akpc806a/CAN_Logger/Firmware/IAR/demos/ARMCM4-STM32F407-DISCOVERY/main.c

/*
    ChibiOS/RT - Copyright (C) 2006-2013 Giovanni Di Sirio

    Licensed under the Apache License, Version 2.0 (the "License");
    you may not use this file except in compliance with the License.
    You may obtain a copy of the License at

        http://www.apache.org/licenses/LICENSE-2.0

    Unless required by applicable law or agreed to in writing, software
    distributed under the License is distributed on an "AS IS" BASIS,
    WITHOUT WARRANTIES OR CONDITIONS OF ANY KIND, either express or implied.
    See the License for the specific language governing permissions and
    limitations under the License.
*/

#include "ch.h"
#include "hal.h"
#include "chprintf.h"

#include "ff.h"

#include "shell.h"


#include "file_utils.h"
#include <time.h>

#include <stdio.h>
#include <limits.h>

//#define INDICATE_IDLE_ON() palSetPad(GPIOA, GPIOA_PIN5_LED_R)
//#define INDICATE_IDLE_OFF() palClearPad(GPIOA, GPIOA_PIN5_LED_R)
#define INDICATE_IDLE_ON()
#define INDICATE_IDLE_OFF()

uint8_t bButton = 0;
unsigned char bLogging = 0; // if =1 than we logging to SD card

//------------------------------------------------------------------------------
// CAN instance configuration
static CANConfig cancfg = {
  CAN_MCR_ABOM | CAN_MCR_AWUM,
  CAN_BTR_SJW(0) | CAN_BTR_TS2(2) |
  CAN_BTR_TS1(1) | CAN_BTR_BRP(13)
};


//------------------------------------------------------------------------------

/*===========================================================================*/
// data bufferization functions

#define SD_WRITE_BUFFER             (1024*49)//(1024*21)   // 21K
#define SD_WRITE_BUFFER_FLUSH_LIMIT (1024*48)//(1024*20)   // 20K

#include <string.h>
#include "mmcsd.h"

// buffer for collecting data to write
char sd_buffer[SD_WRITE_BUFFER];
WORD sd_buffer_length = 0;

// buffer for storing ready to write data
char sd_buffer_for_write[SD_WRITE_BUFFER];
unsigned char bReqWrite = 0; // write request, the sd_buffer is being copied to sd_buffer_for_write 
WORD sd_buffer_length_for_write = 0;

unsigned char bWriteFault = 0; // in case of overlap or write fault


// fill buffer with spaces (before \r\n) to make it 512 byte size
// return 1 if filled and ready to write
int align_buffer()
{
  int i;
  int len;
  
  if (sd_buffer_length < 2) return 0;
  if (sd_buffer[sd_buffer_length-2] != '\r') return 0;
  if (sd_buffer[sd_buffer_length-1] != '\n') return 0;
  
  len = MMCSD_BLOCK_SIZE - (sd_buffer_length % MMCSD_BLOCK_SIZE);
  for (i = 0; i < len; i++)
    sd_buffer[sd_buffer_length + i - 2] = ' ';
  sd_buffer[sd_buffer_length - 2] = ',';
  sd_buffer[sd_buffer_length + len - 2] = '\r';
  sd_buffer[sd_buffer_length + len - 1] = '\n';
  
  sd_buffer_length += len;
  
  return 1;
}

// copy input buffer into the buffer for flash writing data
void copy_buffer()
{
  // request write operation
  memcpy(sd_buffer_for_write, sd_buffer, sd_buffer_length);
  sd_buffer_length_for_write = sd_buffer_length;
  sd_buffer_length = 0;
}

void request_write()
{
  chSysLock(); // prevent re-entry
  
  if (bReqWrite)
    bWriteFault = 1; // buffer overlapping
  
  // request write operation
  align_buffer();
  copy_buffer();
  bReqWrite = 1;
  
  chSysUnlock(); // leaving critical section
}

int iLastWriteSecond = 0;
static struct tm timp;
  
void fwrite_string(char *pString)
{
  WORD length = strlen(pString);

  // Add string
  memcpy(&sd_buffer[sd_buffer_length], pString, length);
  sd_buffer_length += length;
  
  // Check flush limit
  if(sd_buffer_length >= SD_WRITE_BUFFER_FLUSH_LIMIT)
  {
    request_write();
  }
}





// file writing 
FATFS SDC_FS;
FIL *file;
FRESULT fres;

int i;
int iSecond;
#define STRLINE_LENGTH 1024
char sLine[STRLINE_LENGTH];
systime_t stLastWriting;
unsigned char bIncludeTimestamp = 1;

void start_log(int file_index, char* file_name)
{
  // open file and write the begining of the load
  if (file_index >= 0)
  {
    sprintf(sLine, "%d.csv", file_index);
  }
  else if (file_name != 0)
  {
    sprintf(sLine, "%s.csv", file_name);
  }
  else
  {
    rtcGetTimeTm(&RTCD1, &timp);        
    sprintf(sLine, "%02d-%02d-%02d.csv", timp.tm_hour, timp.tm_min, timp.tm_sec);
  }
  
  file = fopen_(sLine, "a");
  if (bIncludeTimestamp)
    strcpy(sLine, "Timestamp,ID,Data0,Data1,Data2,Data3,Data4,Data5,Data6,Data7\r\n");
  else
    strcpy(sLine, "ID,Data0,Data1,Data2,Data3,Data4,Data5,Data6,Data7\r\n");
  fwrite_string(sLine);
  align_buffer();
  fwrite_(sd_buffer, 1, sd_buffer_length, file);
  f_sync(file);

  // reset buffer counters
  sd_buffer_length_for_write = 0;
  sd_buffer_length = 0;

  bWriteFault = 0;

  stLastWriting = chTimeNow(); // record time when we did write

  bLogging = 1;
}

int iFilterMask = 0;
int iFilterValue = 0;
unsigned char bLogStdMsgs = 1;
unsigned char bLogExtMsgs = 1;

unsigned char bAutoStart = 0;
unsigned char bCircularWriting = 0;
unsigned char bStartOnCAN = 0;
unsigned char bStopOnCAN = 0;
int iIDStartValue = 0;
int iIDStartMask = 0;
unsigned char bStartFrameToName = 0;
int iIDStopValue = 0;
int iIDStopMask = 0;

int iLastFileName = 0; // the file name index from file 


int read_config_file()
{
  int value;
  char name[128];
  char param[128];
  int baud;
  int res = 0;
  int ack = 0;
  
  iFilterMask = 0;
  iFilterValue = 0;
  bIncludeTimestamp = 1;
  bLogStdMsgs = 1;
  bLogExtMsgs = 1;
  
  
  // read file
  file = fopen_("Config.txt", "r");
  if (file == 0) 
  {
    return 0;
  }
  
  while( f_gets(sLine, STRLINE_LENGTH, file) )
  {
    if (sscanf(sLine, "%s %s", name, param) == 0)
    {
      continue;
    }
    
    if (strcmp(name, "baud") == 0)
    {
      if (sscanf(param, "%d", &value) == 0) continue;

      baud = value;
      res = 1; // at least we got baudrate, config file accepted
    }
    else
    if (strcmp(name, "ack_en")  == 0)
    {
      if (sscanf(param, "%d", &value) == 0) continue;
      
      ack = value;
    }
    else
    if (strcmp(name, "id_filter_mask")  == 0)
    {
      if (sscanf(param, "%x", &value) == 0) continue;
      
      iFilterMask = value;
    }
    else
    if (strcmp(name, "id_filter_value")  == 0)
    {
      if (sscanf(param, "%x", &value) == 0) continue;
      
      iFilterValue = value;
    }
    else
    if (strcmp(name, "timestamp")  == 0)
    {
      if (sscanf(param, "%d", &value) == 0) continue;
      
      bIncludeTimestamp = value;
    }
    else
    if (strcmp(name, "log_std")  == 0)
    {
      if (sscanf(param, "%d", &value) == 0) continue;
      
      bLogStdMsgs = value;
    }
    else
    if (strcmp(name, "log_ext")  == 0)
    {
      if (sscanf(param, "%d", &value) == 0) continue;
      
      bLogExtMsgs = value;
    }
    else
    if (strcmp(name, "start_on_power")  == 0)
    {
      if (sscanf(param, "%d", &value) == 0) continue;
      
      bAutoStart = value;
    }
    else
    if (strcmp(name, "circular_write")  == 0)
    {
      if (sscanf(param, "%d", &value) == 0) continue;
      
      bCircularWriting = value;
    }
    else
    if (strcmp(name, "start_id_value")  == 0)
    {
      if (sscanf(param, "%x", &value) == 0) continue;
      
      iIDStartValue = value;
    }
    else
    if (strcmp(name, "start_id_mask")  == 0)
    {
      if (sscanf(param, "%x", &value) == 0) continue;
      
      iIDStartMask = value;
    }
    else
    if (strcmp(name, "start_frame_to_name")  == 0)
    {
      if (sscanf(param, "%d", &value) == 0) continue;
      
      bStartFrameToName = value;
    }
    else
    if (strcmp(name, "stop_id_value")  == 0)
    {
      if (sscanf(param, "%x", &value) == 0) continue;
      
      iIDStopValue = value;
    }
    else
    if (strcmp(name, "stop_id_mask")  == 0)
    {
      if (sscanf(param, "%x", &value) == 0) continue;
      
      iIDStopMask = value;
    }
    else
    if (strcmp(name, "start_on_CAN")  == 0)
    {
      if (sscanf(param, "%d", &value) == 0) continue;
      
      bStartOnCAN = value;
    }
    else
    if (strcmp(name, "stop_on_CAN")  == 0)
    {
      if (sscanf(param, "%d", &value) == 0) continue;
      
      bStopOnCAN = value;
    }
  }
  
  // configure CAN
  baud = (int)(7*1000.0/((float)(baud)) + 0.5); // prescaler value  
  if (ack)
    cancfg.btr =  CAN_BTR_SJW(0) | CAN_BTR_TS2(2) | CAN_BTR_TS1(1) | CAN_BTR_BRP(baud - 1);
  else
    cancfg.btr =  CAN_BTR_SJW(0) | CAN_BTR_TS2(2) | CAN_BTR_TS1(1) | CAN_BTR_BRP(baud - 1) | CAN_BTR_SILM; // silent mode flag
  canStop(&CAND2);
  canStart(&CAND2, &cancfg);
  fclose_(file);
    
  return res;
}



// parse line of log to playback
int parse_line(char *s, CANTxFrame* txmsg, uint32_t* iTimeStamp)
{
  int iCount = 0;
  int iValue = 0;
  char * sStart = s;
  char * sNext = s;
  
  // converting the time stamp
  *iTimeStamp = strtol(sStart, &sNext, 10);
  if (*sNext != ',') return 0; // spelling error
  sStart = sNext+1;
//printf("%d\r\n", *iTimeStamp);
  
  // converting id
  txmsg->EID = strtol(sStart, &sNext, 16);
  if (*sNext != ',') return 0; // spelling error
  sStart = sNext+1;
//printf("%d\r\n", txmsg->EID);
  
  // converting data
  for (iCount = 0; iCount < 8; iCount++)
  {
    iValue = strtol(sStart, &sNext, 16);
    if (sNext == sStart) 
      break;
    else
      txmsg->data8[iCount] = iValue;
    
    sStart = sNext+1;
    
//printf("%x\r\n", txmsg->data8[iCount]);
  }
  
  txmsg->DLC = iCount;
  
  return 1;
  
}

// play recorded file
int read_playback_file()
{
  CANTxFrame txmsg;
  uint32_t iTimeMessage = 0;
  uint32_t iTimeStart;
  uint32_t iTimeOffst = 0;
  int32_t iDelay = 0;
  
  // read file
  file = fopen_("Play.csv", "r");
  if (file == 0)
  {
    return 0;
  }
  
  palClearPad(GPIOA, GPIOA_PIN7_LED_G);
  
  f_gets(sLine, STRLINE_LENGTH, file); // always skip first line (header)
  
  txmsg.RTR = 0; // only data frames
  iTimeStart = chTimeNow();
  
  // there is Play.csv on SD folder -- playback mode
  while( f_gets(sLine, STRLINE_LENGTH, file) )
  {
    if (parse_line(sLine, &txmsg, &iTimeMessage))
    {
      // if it doesnt fit to standard ID (or enforced extended ID format)
      if (txmsg.EID > 0x7FF || bLogStdMsgs == 0)
        txmsg.IDE = 1;
      else
        txmsg.IDE = 0;
      
      if (iTimeOffst == 0) 
        iTimeOffst = iTimeMessage; // this is first message from file

      iTimeMessage -= iTimeOffst; // first message now has time 0
      iDelay = iTimeMessage - (chTimeNow() - iTimeStart); // how much we should wait
      if (iDelay > 0) 
        chThdSleepMilliseconds(iDelay); // delay to maintain timestamps
      
      if (canTransmit(&CAND2, 1, &txmsg, 50) != RDY_OK) // sending with 50 ms time-out
        palSetPad(GPIOA, GPIOA_PIN5_LED_R); // transmission error indication
      
      palTogglePad(GPIOA, GPIOA_PIN6_LED_B);
    }
  }
  
  fclose_(file);
  
  palSetPad(GPIOA, GPIOA_PIN7_LED_G);
  palClearPad(GPIOA, GPIOA_PIN6_LED_B);
  
  return 1;
}

#define MAX_FILE_NAME 99999999
int iMinFileName = INT_MAX;
int iMaxFileName = -1;

FRESULT scan_files (char* path)
{
    FRESULT res;
    DIR dir;
    //UINT i;
    static FILINFO fno;
    static char lfname[256];
    char name[128];
    char ext[64];
    int iFileName = 0;
    int iGapStart = 0;
    int iGapEnd = MAX_FILE_NAME;


    res = f_opendir(&dir, path);                       /* Open the directory */
    if (res == FR_OK) 
    {
        for (;;) 
        {
            res = f_readdir(&dir, &fno);                   /* Read a directory item */
            if (res != FR_OK || fno.fname[0] == 0) break;  /* Break on error or end of dir */
            if (fno.fattrib & AM_DIR) 
            {                    
              /* It is a directory */
            } 
            else 
            {                                       
                /* It is a file. */
                if (sscanf(fno.fname, "%[^.].%s", name, ext) != 0)
                {
                  // we can separate file name into name.ext
                  if (strcmp(ext, "csv") == 0)
                  {
                    // if it is csv file
                    if (sscanf(name, "%d", &iFileName) != 0)
                    {
                      if (iFileName < MAX_FILE_NAME - iFileName)
                      {
                        // iFileName is closer to 0 than to MAX_FILE_NAME
                        if (iGapStart < iFileName)
                          iGapStart = iFileName;
                      }
                      else
                      {
                        // iFileName is closer to MAX_FILE_NAME than to 0
                        if (iGapEnd > iFileName)
                          iGapEnd = iFileName;
                      }
                        
                      // the name is a digit
                      if (iFileName > iMaxFileName) iMaxFileName = iFileName;
                      if (iFileName < iMinFileName) iMinFileName = iFileName;
                    }
                  }
                }
                //printf("%s/%s\n", path, fno.fname);
            }
        }
        //f_closedir(&dir);
    }
    
    // special case when we rolled over max file name in cyclic writing
    if (iMinFileName == 0 && iMaxFileName == MAX_FILE_NAME)
    {
      iMinFileName = iGapEnd;
      iMaxFileName = iGapStart;
    }

    return res;
}


int init_sd()
{
  // initializing SDC interface
  sdcStart(&SDCD1, NULL);
  if (sdcConnect(&SDCD1) == CH_FAILED) 
  {
    return 0;
  }
  
  // mount the file system
  fres = f_mount(0, &SDC_FS);
  if (fres != FR_OK)
  {
    sdcDisconnect(&SDCD1);
    return 0;
  }
  
  // trying just dummy read file
  file = fopen_("Config.txt", "r");
  if (file)
    fclose_(file);

  
  return 1;
}
//------------------------------------------------------------------------------
/*
// 500kb -- work
static const CANConfig cancfg = {
  CAN_MCR_ABOM | CAN_MCR_AWUM,
  CAN_BTR_SJW(0) | CAN_BTR_TS2(2) |
  CAN_BTR_TS1(1) | CAN_BTR_BRP(13)
};
*/

// this is used only when start_frame_to_name=1 for translate CAN message to file name
char sNewFileName[128] = "";

char sTmp[128];

static WORKING_AREA(can1_rx_wa, 256);
static msg_t can1_rx(void *p) {
  EventListener el;
  CANRxFrame rxmsg;

  (void)p;
  chRegSetThreadName("receiver can 1");
  chEvtRegister(&CAND2.rxfull_event, &el, 0);
  while(!chThdShouldTerminate()) 
  {
    // if (chEvtWaitAnyTimeout(ALL_EVENTS, MS2ST(100)) == 0) continue;
    chEvtWaitAny(ALL_EVENTS);
    
    while (canReceive(&CAND2, CAN_ANY_MAILBOX, &rxmsg, TIME_IMMEDIATE) == RDY_OK) 
    {
      /* Process message.*/
      
      if (!bLogging && bStartOnCAN)
      {
        // should we start?
        if (rxmsg.IDE == 0) // if STD then just copy standard to extended ID
          rxmsg.EID = rxmsg.SID;

        // then check filter conditions
        if ((rxmsg.EID & iIDStartMask) == (iIDStartValue & iIDStartMask)) 
        {
          bButton = 1; // TODO: this one is very dirty way to start a log :)
          if (bStartFrameToName)
          {
            sNewFileName[0] = 0;
            for (i = 0; i < rxmsg.DLC; i++)
              sprintf(sNewFileName+strlen(sNewFileName), "%01X", (rxmsg.data8[i])&0xF);
          }
        }
      }
      
      if (bLogging)
      {
        // checking message acceptance
        if (rxmsg.IDE)
        {
          // message with extended ID received
          
          // are we accepting extended ID?
          if (!bLogExtMsgs) continue; 

          // then check filter conditions
          if ((rxmsg.EID & iFilterMask) != (iFilterValue & iFilterMask)) continue;
        }
        else
        {
          // message with standard ID received
          
          // are we accepting standard ID?
          if (!bLogStdMsgs) continue;

          // then check filter conditions
          if ((rxmsg.SID & iFilterMask) != (iFilterValue & iFilterMask)) continue;
		  
          rxmsg.EID = rxmsg.SID; // this is because we are writing value from extended ID
        }

        // write down data
        if (bIncludeTimestamp)
          sprintf(sTmp, "%d,%X", chTimeNow(), rxmsg.EID);
        else
          sprintf(sTmp, "%X", rxmsg.EID);
        
        for (i = 0; i < rxmsg.DLC; i++)
        {
          sprintf(sTmp+strlen(sTmp), ",%02X", rxmsg.data8[i]);
        }

        strcat(sTmp, "\r\n");
        fwrite_string(sTmp);
        
        // should we stop?
        if (bStopOnCAN)
        {
          if (rxmsg.IDE == 0) // if STD then just copy standard to extended ID
            rxmsg.EID = rxmsg.SID;

          // then check filter conditions
          if ((rxmsg.EID & iIDStopMask) == (iIDStopValue & iIDStopMask)) 
          {
            bLogging = 0;
            // we are in logging state -- should write the rest of the log
            request_write();
          }
        }
      }
      
      palTogglePad(GPIOA, GPIOA_PIN7_LED_G);
    }
  }
  chEvtUnregister(&CAND2.rxfull_event, &el);
  return 0;
}

//------------------------------------------------------------------------------
int iButtonStableCounter = 0;
unsigned char bButtonNew = 0;
unsigned char bButtonPrev = 0;
#define BUTTON_COUNTER_THRESHOLD 50000

char sName[128];
/*
 * Application entry point.
 */
int main(void) 
{
  //CANTxFrame txmsg;
  
  halInit();
  chSysInit();
  
  palSetPad(GPIOA, GPIOA_PIN7_LED_G);
 
  //canSTM32SetFilters(0, 0, NULL);
  canStart(&CAND1, &cancfg);
  canStart(&CAND2, &cancfg);
  chThdCreateStatic(can1_rx_wa, sizeof(can1_rx_wa), NORMALPRIO + 7, can1_rx, NULL);


  // first -- let us try to open SD card, maybe there is something interesting there
  if (init_sd()) // trying to initialize sd card
  {
    if (read_config_file()) // trying to read configuration file
    {
      // maybe there is playback mode?
      if (bAutoStart)
        read_playback_file();
      
      // scanning files to determine range of file names 
      scan_files("");
      
      // start loging if we need to do it after power on
      if (bAutoStart)
      {
        // iMaxFileName
        iMaxFileName++;
        if (iMaxFileName > MAX_FILE_NAME) iMaxFileName = 0;
        start_log(iMaxFileName, 0);
      }
    }
  }

  i = 0;
  while (TRUE) 
  {
INDICATE_IDLE_ON();
    
    // maybe we need to write log, because we didnt for long time?
    if (chTimeElapsedSince(stLastWriting) > S2ST(2))
    {
      if (sd_buffer_length > 0) // there is data to write
      {
        // request write operation
        request_write();
      }
    }
    
    if (bReqWrite)
    {
      //palSetPad(GPIOD, GPIOD_PIN_15_BLUELED);
INDICATE_IDLE_OFF();
      if (bCircularWriting)
      {
        // we need to check free space and delete old files
        FATFS *fs;
        DWORD fre_clust, fre_sect, tot_sect;

        fs = &SDC_FS;
        if (f_getfree(0, &fre_clust, &fs) == 0)
        {
          tot_sect = (fs->n_fatent - 2) * fs->csize;
          fre_sect = fre_clust * fs->csize;
          
          // if disk is close to full
          if (fre_sect/((float)(tot_sect)) < 0.1F)
          {
            // erase one old file
            sprintf(sName, "%d.csv", iMinFileName);
            f_unlink(sName);
            iMinFileName++;
            if (iMinFileName > MAX_FILE_NAME) iMaxFileName = 0;
          }
        }
      }
      

      if (fwrite_(sd_buffer_for_write, 1, sd_buffer_length_for_write, file) != sd_buffer_length_for_write)
        bWriteFault = 2;
      if (f_sync(file) != FR_OK)
        bWriteFault = 2;
INDICATE_IDLE_ON();        
      bReqWrite = 0;
      
      stLastWriting = chTimeNow(); // record time when we did write
      
      //palClearPad(GPIOD, GPIOD_PIN_15_BLUELED);
    }
    
    // start-stop log button handling
    if (bButton && bButtonPrev == 0)
    {
      if (bLogging)
      {
        bLogging = 0;
        
        // we are in logging state -- should write the rest of log
        request_write();
        
        if (bStartFrameToName) strcpy(sNewFileName, ""); // empty file name
      }
      else
      {
        palClearPad(GPIOA, GPIOA_PIN5_LED_R);
        palClearPad(GPIOA, GPIOA_PIN6_LED_B); 
        
        // we are not logging -- opening SD card and starting log
        if (init_sd()) // trying to initialize sd card
        {
          if (read_config_file()) // trying to read configuration file
          {
            if (bStartOnCAN == 0) // we can skip this in bStartOnCAN mode
            {
              // maybe there is playback mode?
              read_playback_file();            
              // scanning files to determine range of file names 
              scan_files("");
            }
            
            // all done -- should start loging
            
            // if we are using CAN frame as name
            if (bStartFrameToName && sNewFileName[0] != 0) 
            {
              // file name in sNewFileName should be stored before
              start_log(-1, sNewFileName); 
            }
            else
            {
              // iMaxFileName -- used as file name
              iMaxFileName++;
              if (iMaxFileName > MAX_FILE_NAME) iMaxFileName = 0;
              start_log(iMaxFileName, 0);
            }

          }
          else
          {
            palSetPad(GPIOA, GPIOA_PIN5_LED_R);
            palSetPad(GPIOA, GPIOA_PIN6_LED_B);
          }
        }
        else
          palSetPad(GPIOA, GPIOA_PIN5_LED_R);
      }
    }
    bButtonPrev = bButton;  
    
    // this loop is going very fast, so the button filtering is needed
    bButtonNew = palReadPad(GPIOA, GPIOA_PIN2_BTN);
    if (bButtonNew && bButton == 0)
    {
      iButtonStableCounter++;
      if (iButtonStableCounter > BUTTON_COUNTER_THRESHOLD)
      {
        iButtonStableCounter = 0;
        bButton = 1;
      }
    }
    else
    if (bButtonNew == 0 && bButton)
    {
      iButtonStableCounter++;
      if (iButtonStableCounter > BUTTON_COUNTER_THRESHOLD)
      {
        iButtonStableCounter = 0;
        bButton = 0;
      }
    }
    else
      iButtonStableCounter = 0;
    
    if (bWriteFault)
      palSetPad(GPIOA, GPIOA_PIN5_LED_R);

  }
}
//------------------------------------------------------------------------------
